duelpadarcade/Duelpad-Zen/source/configs/ergoSHIFTRev2/assets/ergoSHIFT-rev2-bare1.jpg

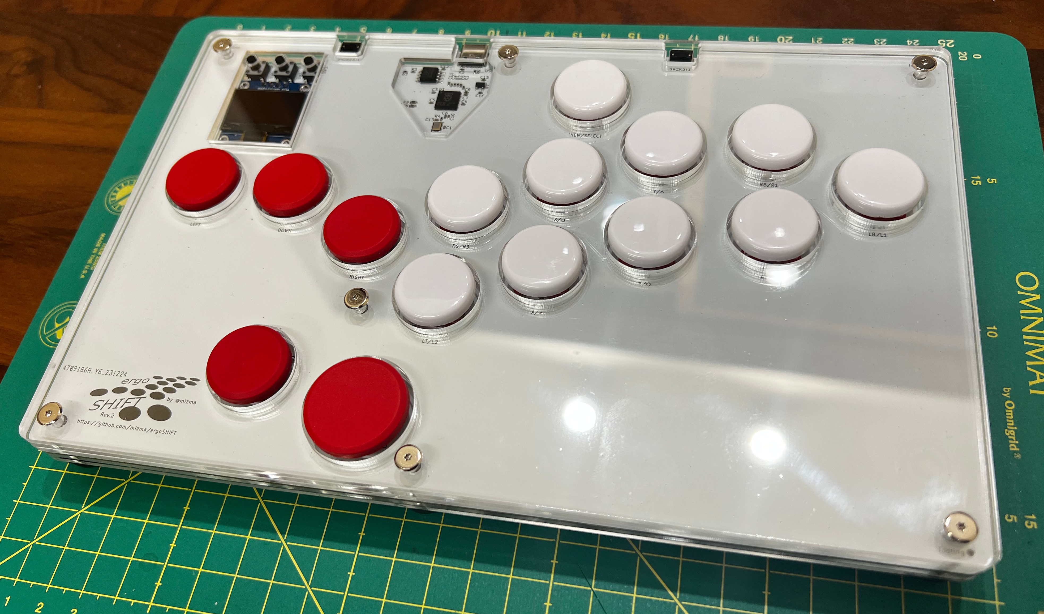
source/configs/ergoSHIFTRev2/assets/ergoSHIFT-rev2-bare1.jpg
