duelpadarcade/Duelpad-Zen/source/configs/Granola/assets/granola-trailmix.png

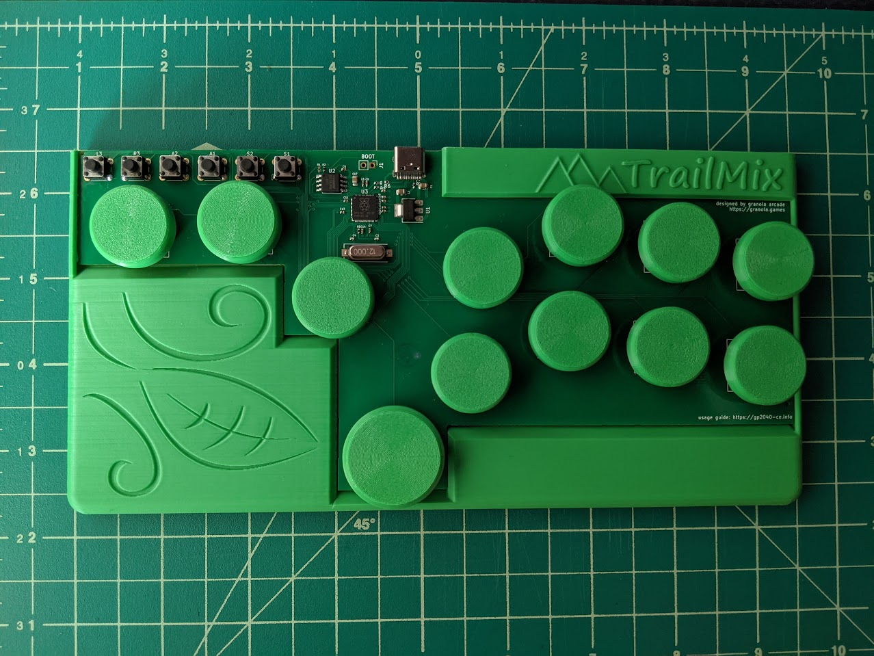
source/configs/Granola/assets/granola-trailmix.png
