duelpadarcade/Duelpad-Zen/source/configs/ARCController/assets/ARC Accessibility Controller 1.JPG

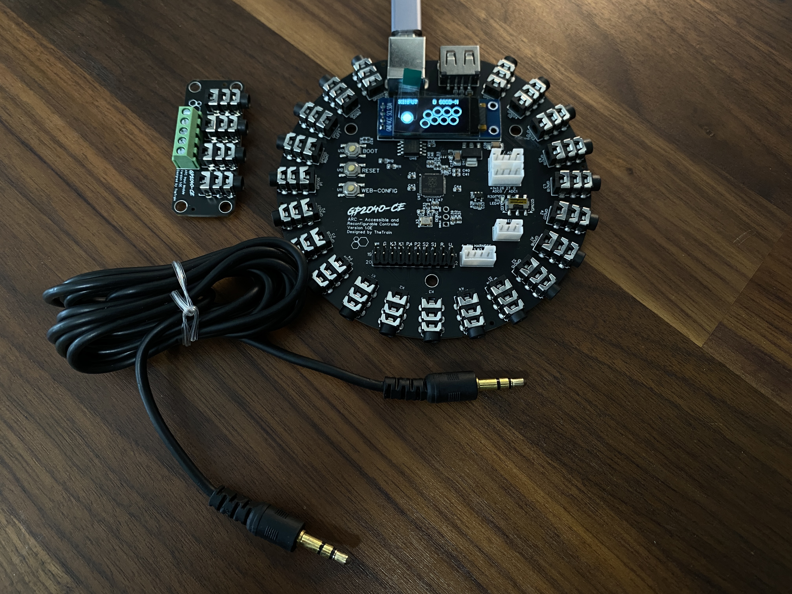
source/configs/ARCController/assets/ARC Accessibility Controller 1.JPG
