duelpadarcade/Duelpad-Zen/source/configs/ARCController/assets/ARC Accessibility Controller 2.JPG

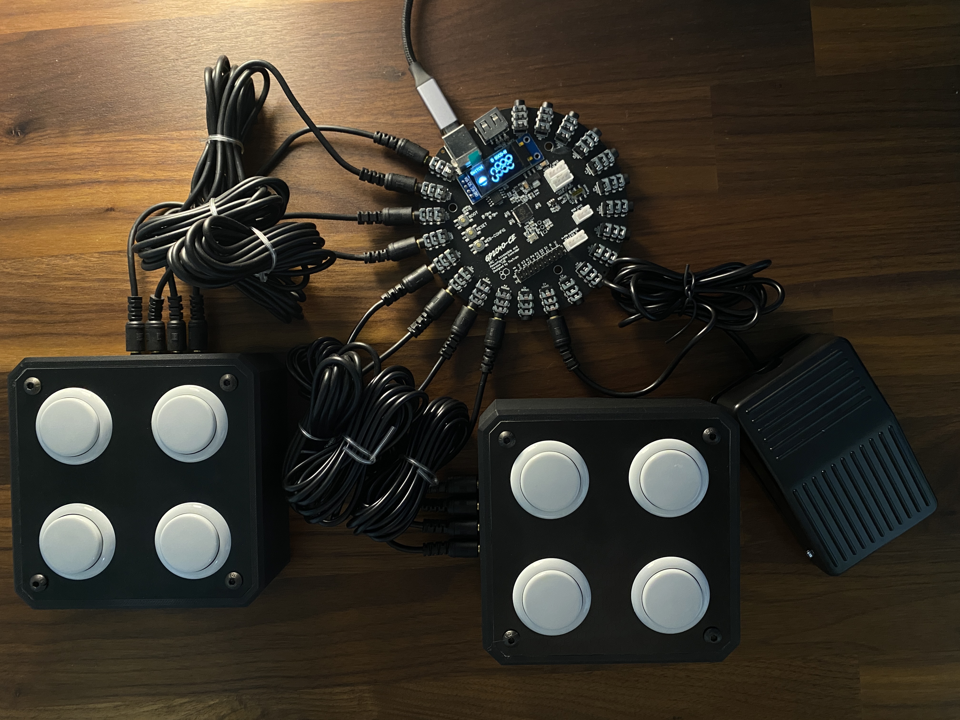
source/configs/ARCController/assets/ARC Accessibility Controller 2.JPG
