duelpadarcade/Duelpad-Zen/source/configs/ARCController/assets/ARC Accessibility Controller 3.JPG

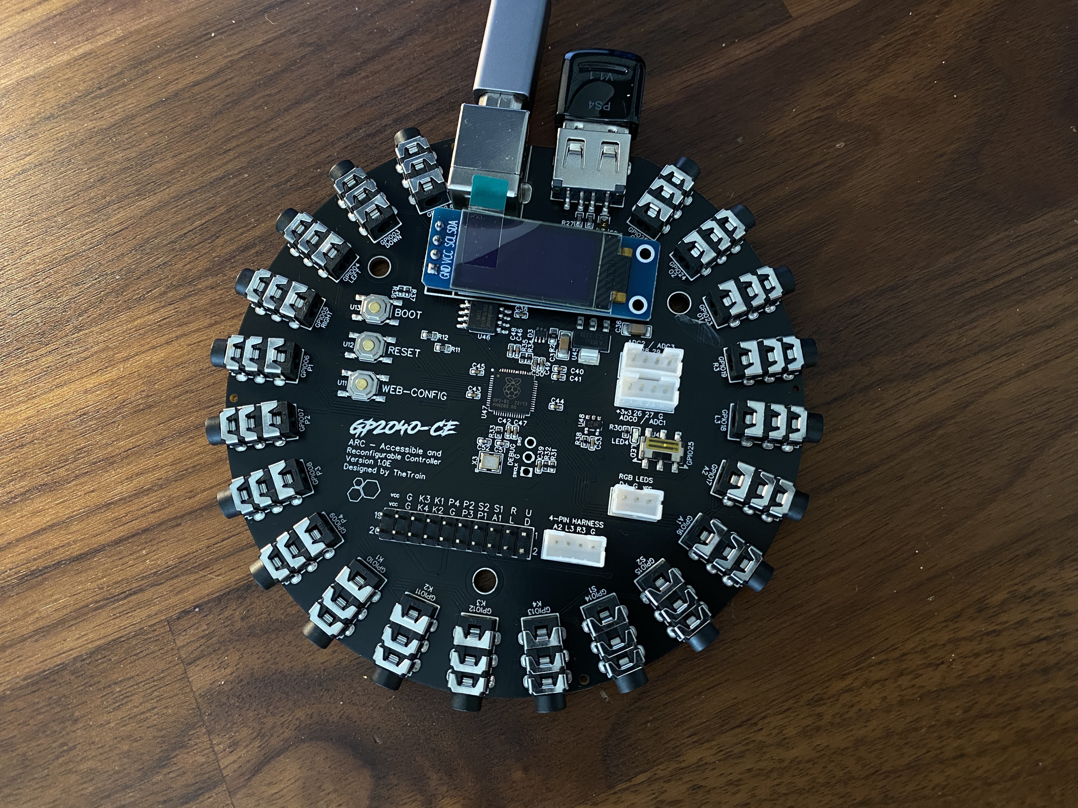
source/configs/ARCController/assets/ARC Accessibility Controller 3.JPG
