duelpadarcade/Duelpad-Zen/source/configs/BentoBox/assets/ScrubTier_Large.png

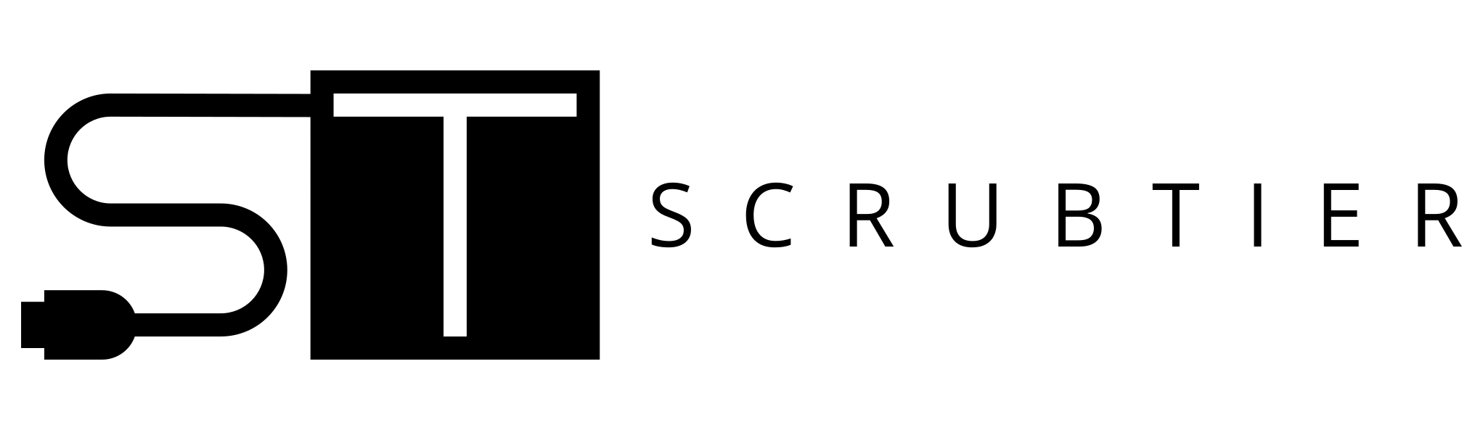
source/configs/BentoBox/assets/ScrubTier_Large.png
