duelpadarcade/Duelpad-Zen/source/configs/BentoBox/assets/ST_BentoBoxV1.png

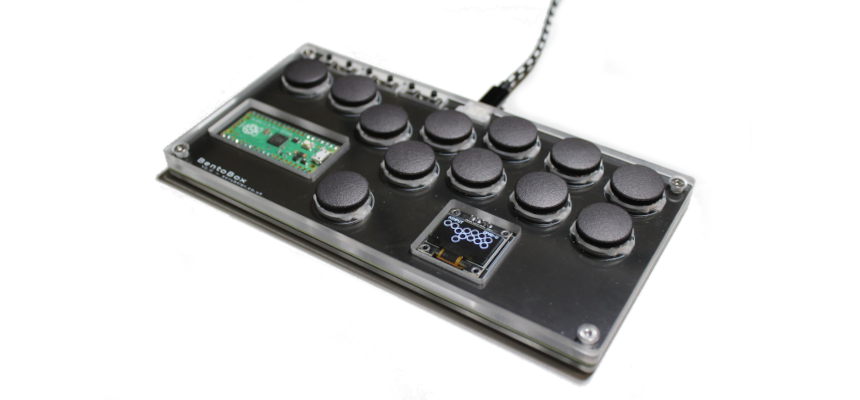
source/configs/BentoBox/assets/ST_BentoBoxV1.png
