duelpadarcade/Duelpad-Zen/source/configs/BentoBox/assets/ST_BentoBoxV2.png

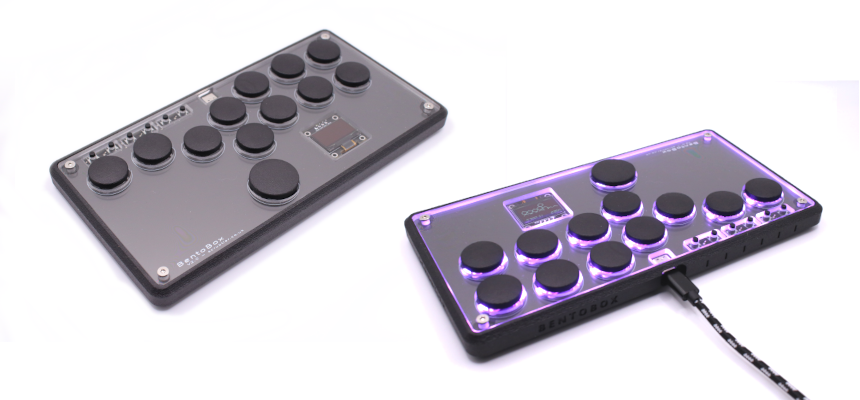
source/configs/BentoBox/assets/ST_BentoBoxV2.png
