duelpadarcade/Duelpad-Zen/source/configs/BentoBox/assets/ST_GGEZStick.png

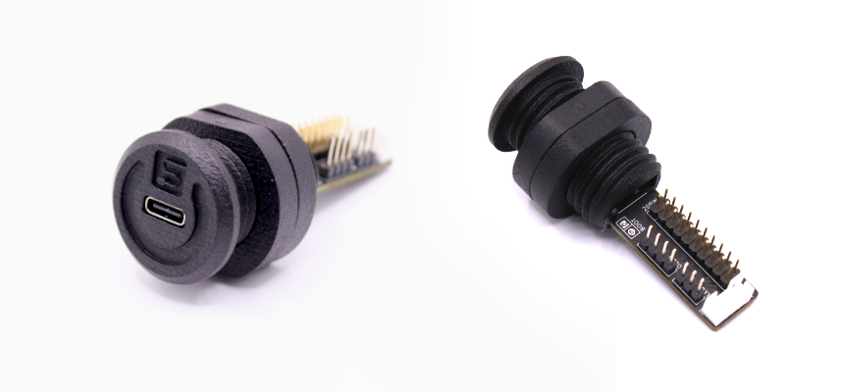
source/configs/BentoBox/assets/ST_GGEZStick.png
