duelpadarcade/Duelpad-Zen/source/configs/ergoSHIFTRev2/assets/ergoSHIFT-rev2-button-mapping.jpg

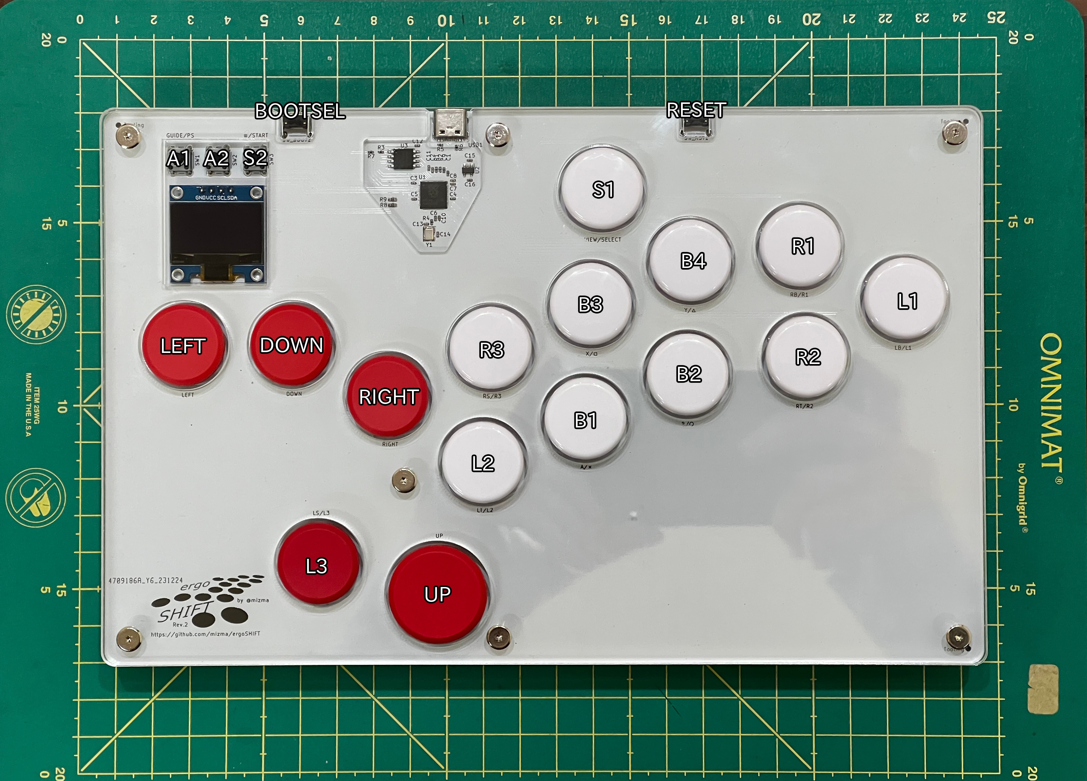
source/configs/ergoSHIFTRev2/assets/ergoSHIFT-rev2-button-mapping.jpg
