duelpadarcade/Duelpad-Zen/source/configs/FightboardV3/assets/FightboardV3.jpg

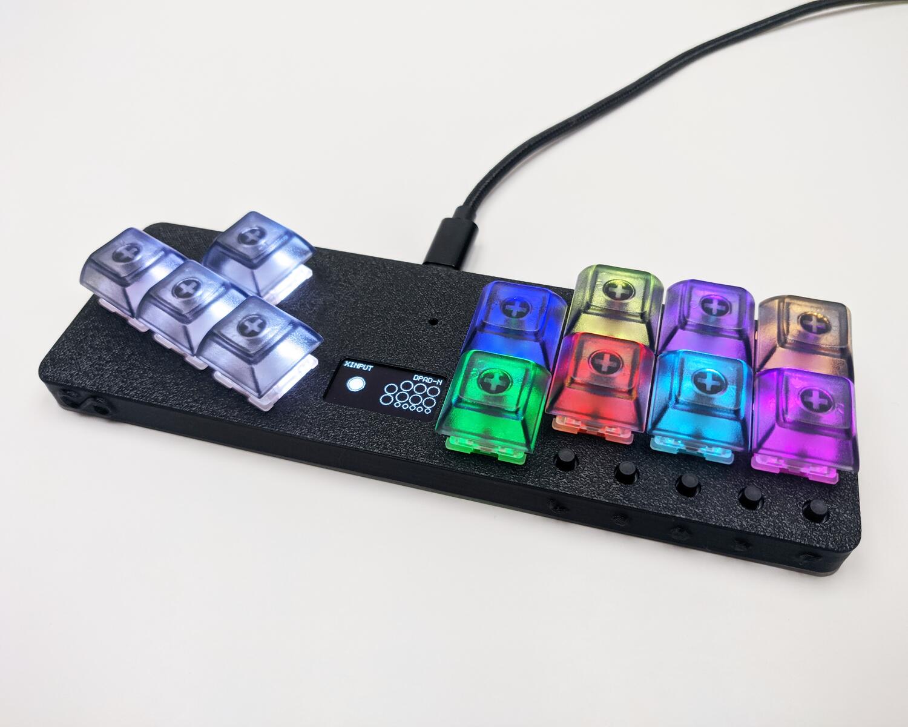
source/configs/FightboardV3/assets/FightboardV3.jpg
