duelpadarcade/Duelpad-Zen/source/configs/FightboardV3Mirrored/assets/FightboardV3Mirrored.jpg

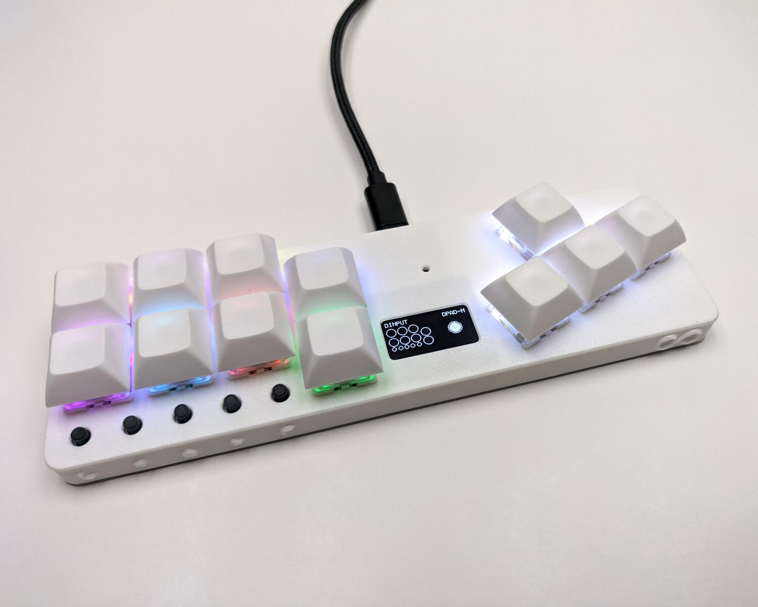
source/configs/FightboardV3Mirrored/assets/FightboardV3Mirrored.jpg
