duelpadarcade/Duelpad-Zen/source/configs/FlatboxRev5/assets/Flatbox-rev5.jpg

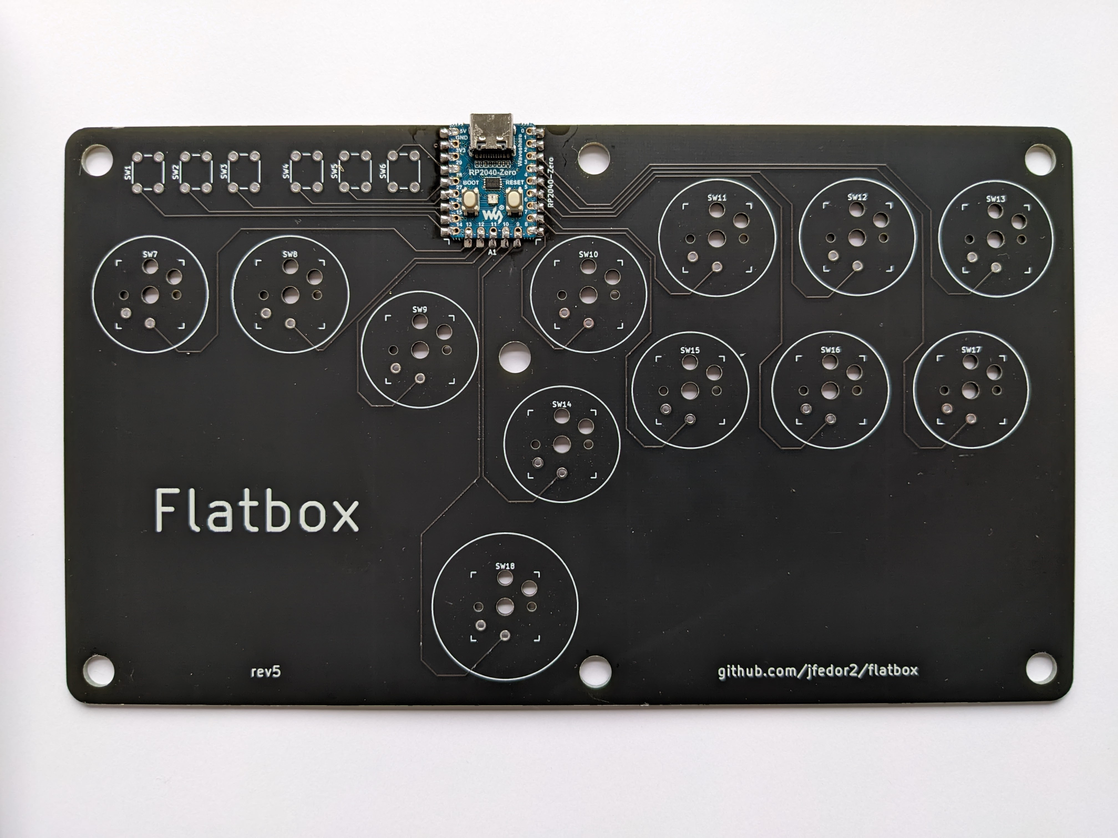
source/configs/FlatboxRev5/assets/Flatbox-rev5.jpg
