duelpadarcade/Duelpad-Zen/source/configs/FlatboxRev5RGB/assets/Flatbox-rev5-rgb.jpg

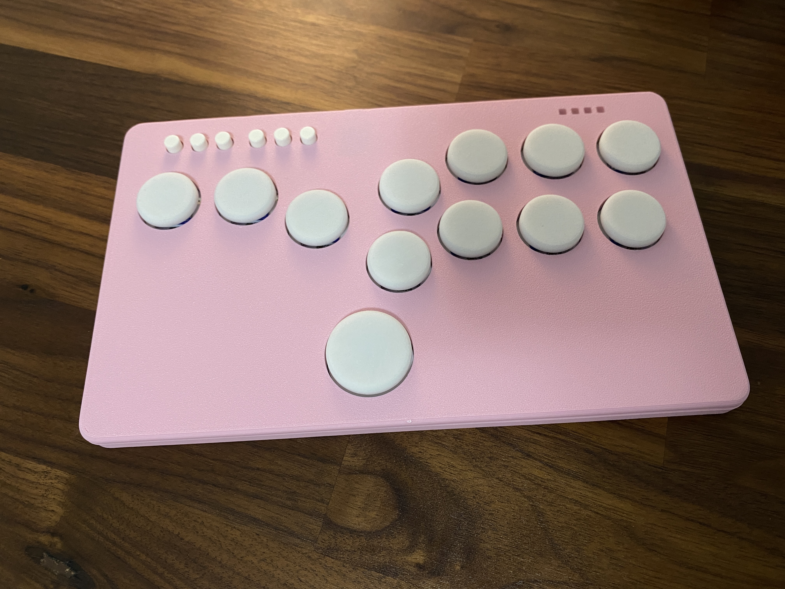
source/configs/FlatboxRev5RGB/assets/Flatbox-rev5-rgb.jpg
