duelpadarcade/Duelpad-Zen/source/configs/FlatboxRev5Southpaw/assets/Flatbox-rev5.jpg

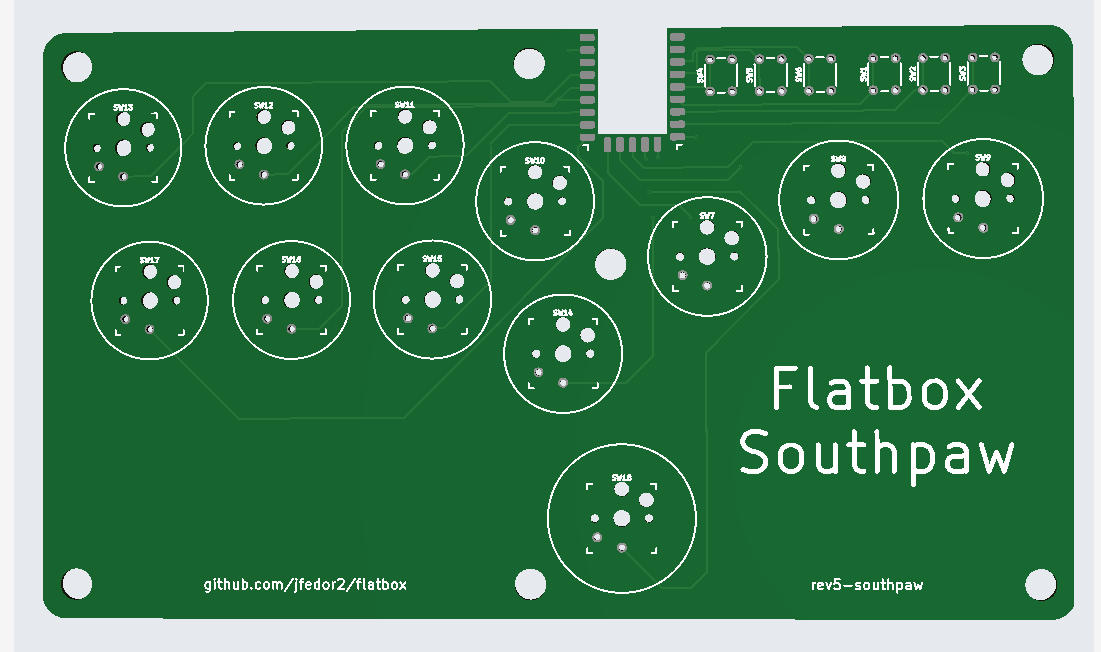
source/configs/FlatboxRev5Southpaw/assets/Flatbox-rev5.jpg
