duelpadarcade/Duelpad-Zen/source/configs/FlatboxRev5USBPassthrough/assets/Flatbox-rev5-USB-Passthrough.jpg

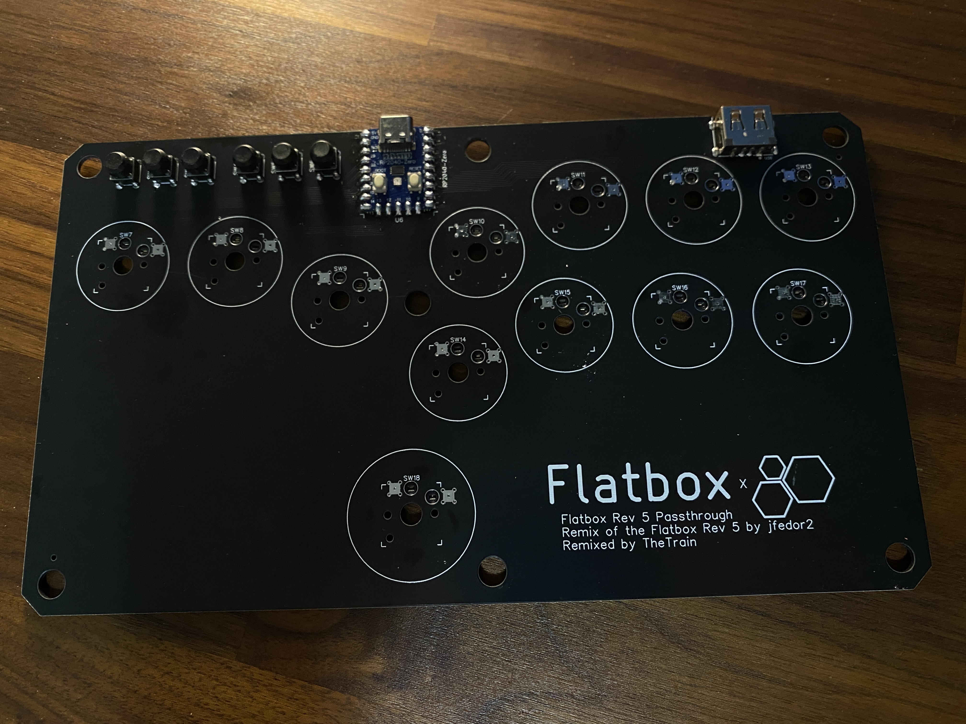
source/configs/FlatboxRev5USBPassthrough/assets/Flatbox-rev5-USB-Passthrough.jpg
