duelpadarcade/Duelpad-Zen/source/configs/Granola/assets/granola-summit.png

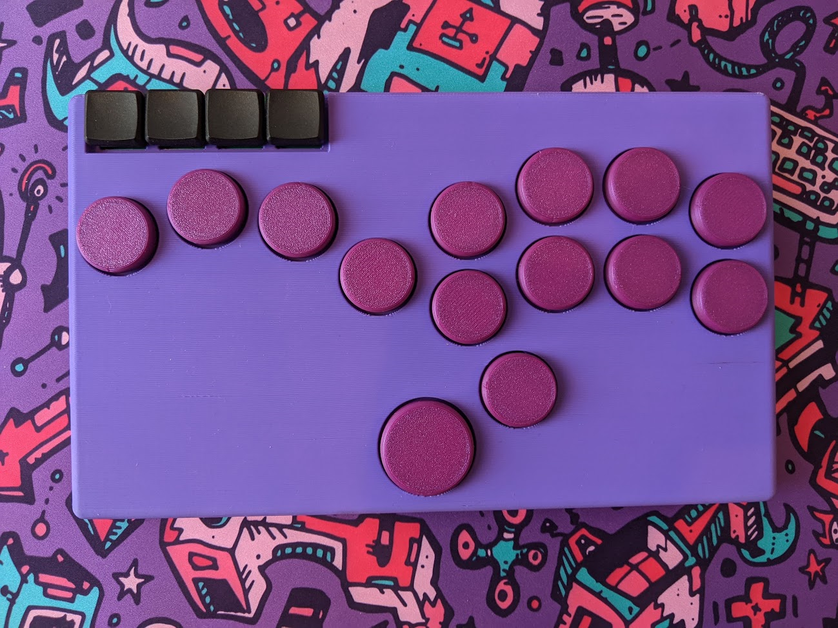
source/configs/Granola/assets/granola-summit.png
