duelpadarcade/Duelpad-Zen/source/configs/Haute42COSMOX/assets/Haute42_G12.png

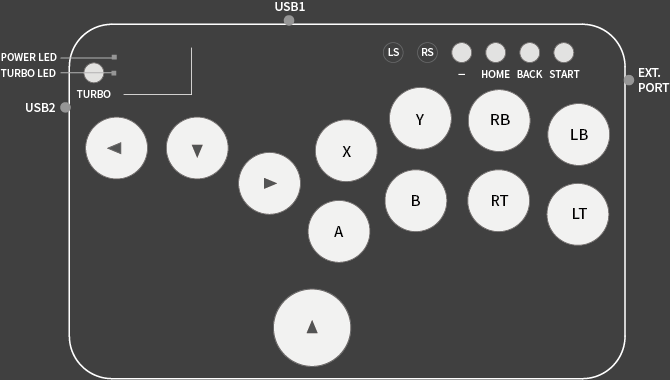
source/configs/Haute42COSMOX/assets/Haute42_G12.png
