duelpadarcade/Duelpad-Zen/source/configs/Haute42COSMOX/assets/Haute42_G13.png

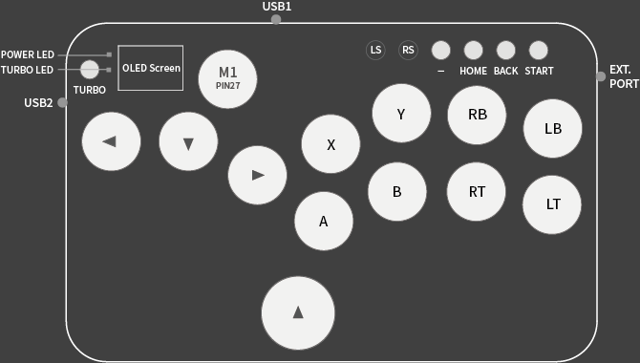
source/configs/Haute42COSMOX/assets/Haute42_G13.png
