duelpadarcade/Duelpad-Zen/source/configs/Haute42COSMOX/assets/Haute42_G16.png

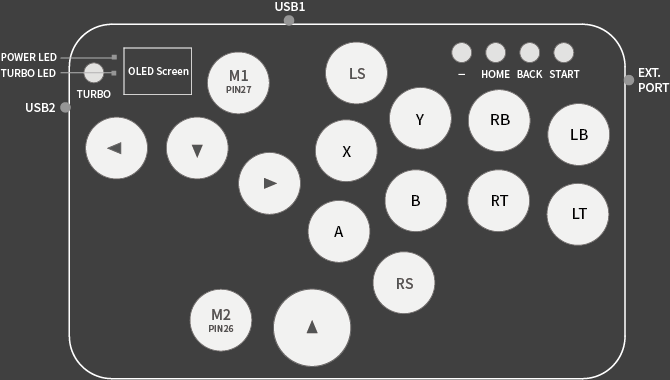
source/configs/Haute42COSMOX/assets/Haute42_G16.png
