duelpadarcade/Duelpad-Zen/source/configs/Haute42COSMOX/assets/Haute42_G_series.png

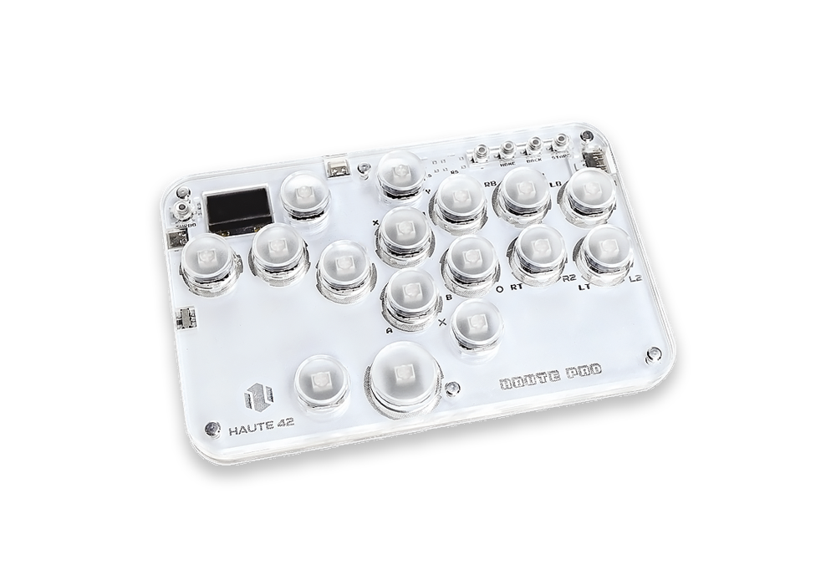
source/configs/Haute42COSMOX/assets/Haute42_G_series.png
