duelpadarcade/Duelpad-Zen/source/configs/Haute42COSMOX/assets/Haute42_Mini.png

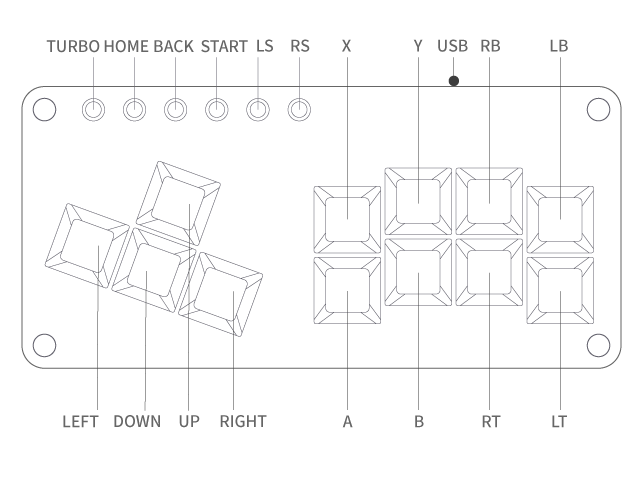
source/configs/Haute42COSMOX/assets/Haute42_Mini.png
