duelpadarcade/Duelpad-Zen/source/configs/Haute42COSMOX/assets/Haute42_Mini_series.png

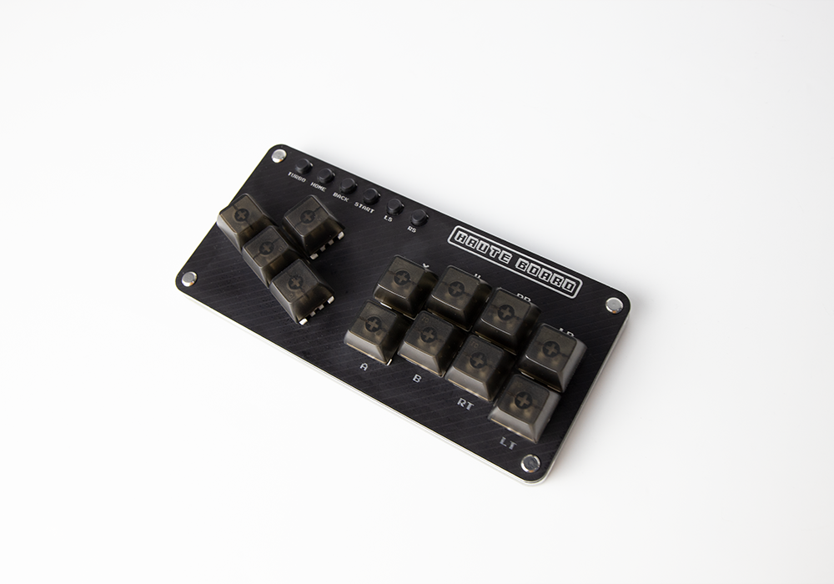
source/configs/Haute42COSMOX/assets/Haute42_Mini_series.png
