duelpadarcade/Duelpad-Zen/source/configs/Haute42COSMOX/assets/Haute42_T13.png

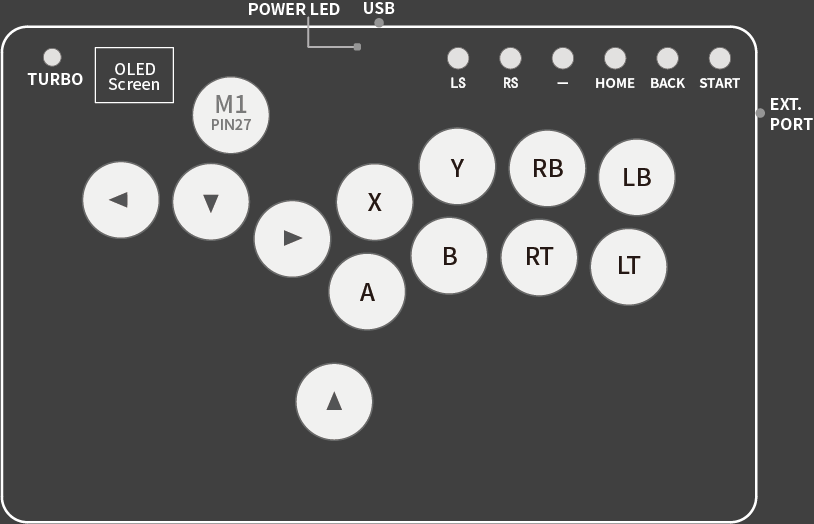
source/configs/Haute42COSMOX/assets/Haute42_T13.png
