duelpadarcade/Duelpad-Zen/source/configs/Haute42COSMOX/assets/Haute42_T16.png

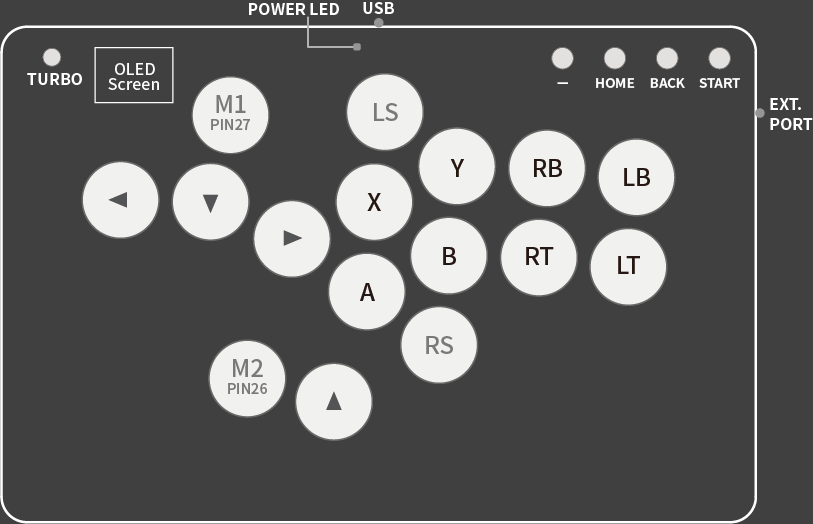
source/configs/Haute42COSMOX/assets/Haute42_T16.png
