duelpadarcade/Duelpad-Zen/source/configs/KB2040/assets/PinMapping.png

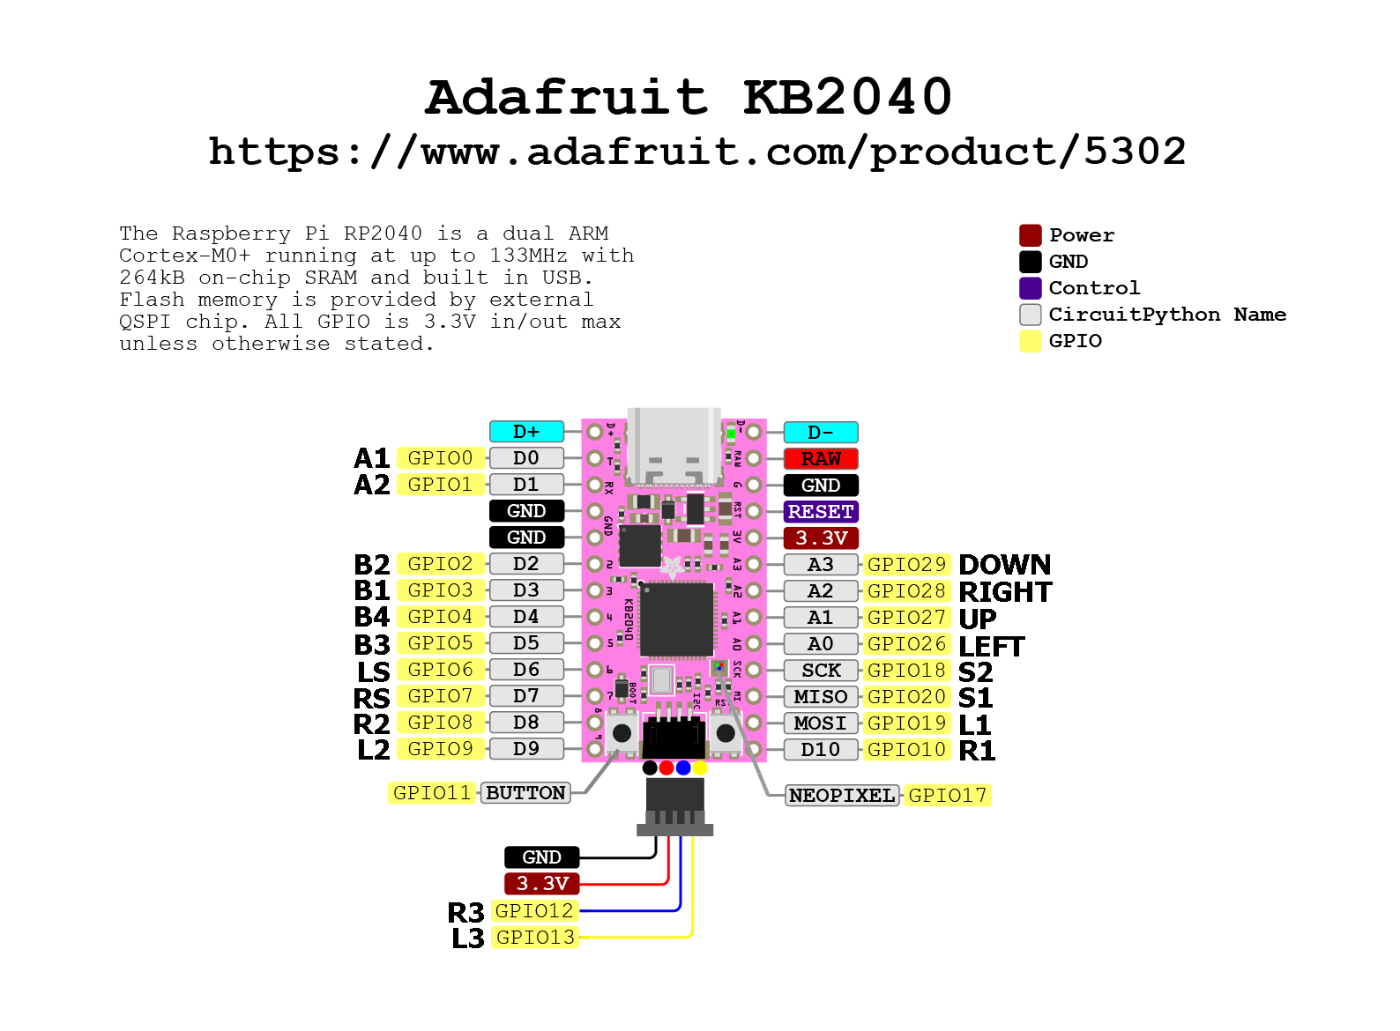
source/configs/KB2040/assets/PinMapping.png
