duelpadarcade/Duelpad-Zen/source/configs/KeyboardConverter/assets/WaveshareRP2040Zero.png

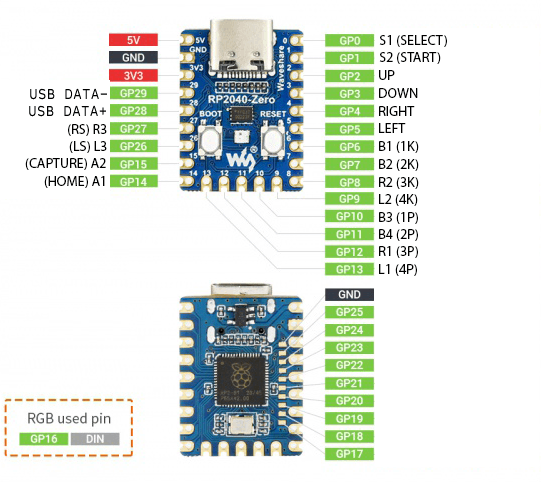
source/configs/KeyboardConverter/assets/WaveshareRP2040Zero.png
