duelpadarcade/Duelpad-Zen/source/configs/Liatris/assets/Liatris.png

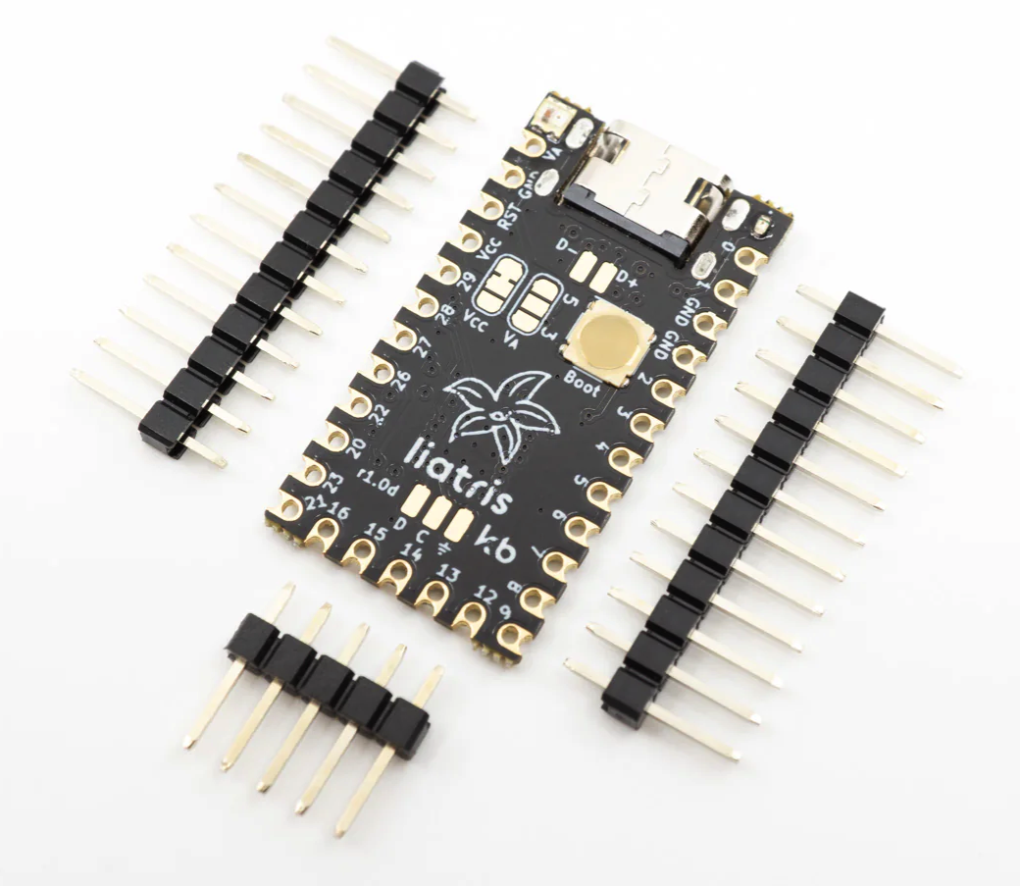
source/configs/Liatris/assets/Liatris.png
