duelpadarcade/Duelpad-Zen/source/configs/MavercadeRev2/assets/Rev2_config_pic.jpg

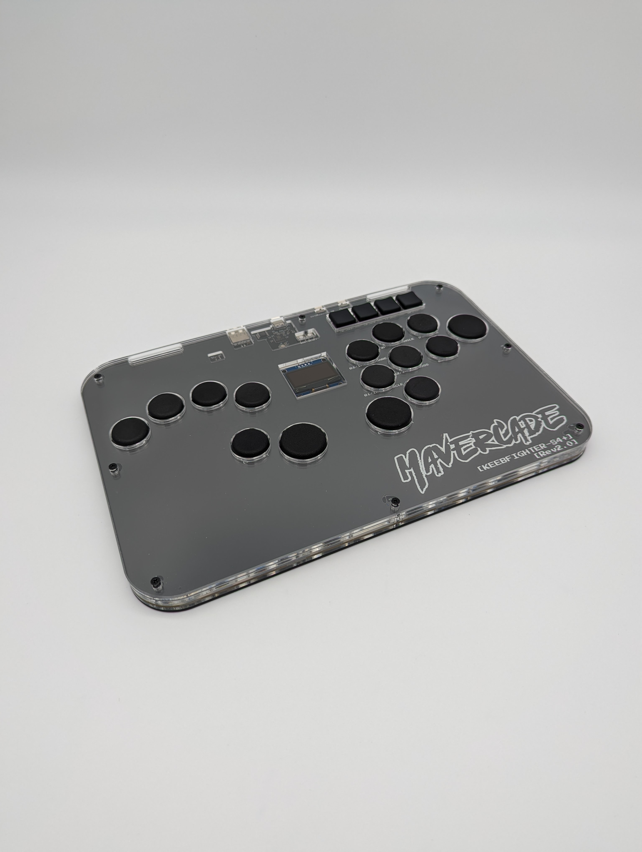
source/configs/MavercadeRev2/assets/Rev2_config_pic.jpg
