duelpadarcade/Duelpad-Zen/source/configs/MiSTercadeV2/assets/MistercadeV2.jpg

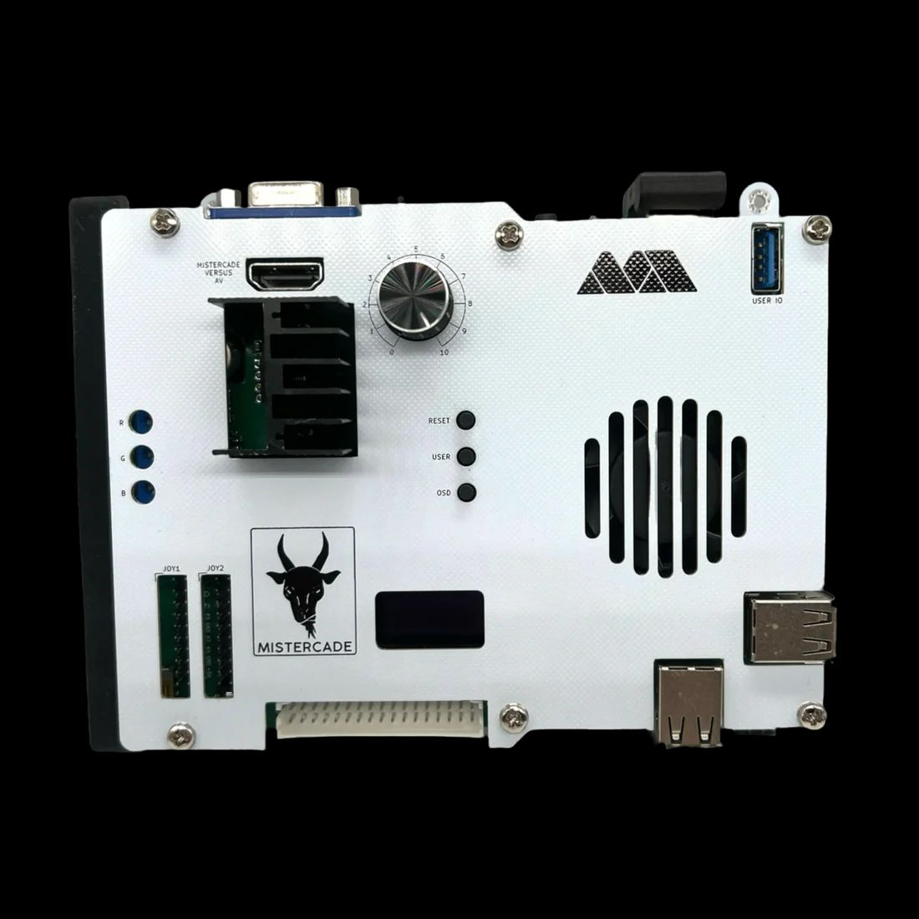
source/configs/MiSTercadeV2/assets/MistercadeV2.jpg
