duelpadarcade/Duelpad-Zen/source/configs/OpenCore0/assets/Open_Core0.jpg

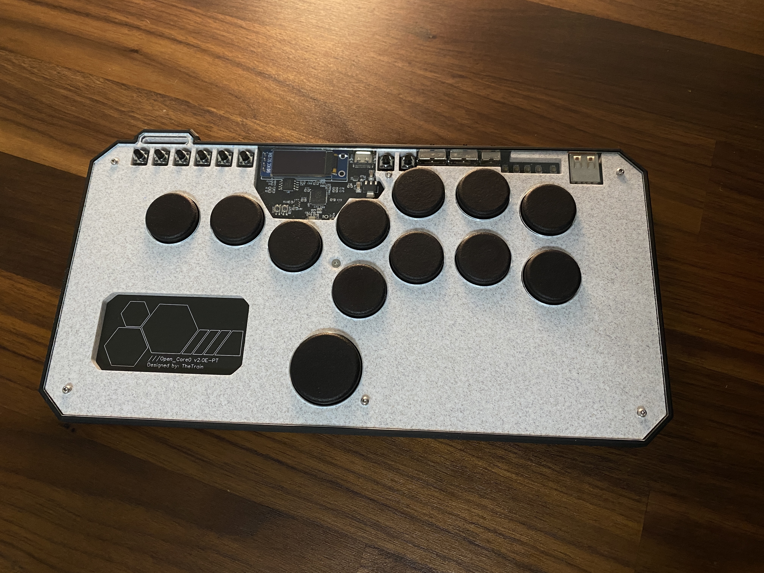
source/configs/OpenCore0/assets/Open_Core0.jpg
