duelpadarcade/Duelpad-Zen/source/configs/OpenCore0/assets/Open_Core0_2.jpg

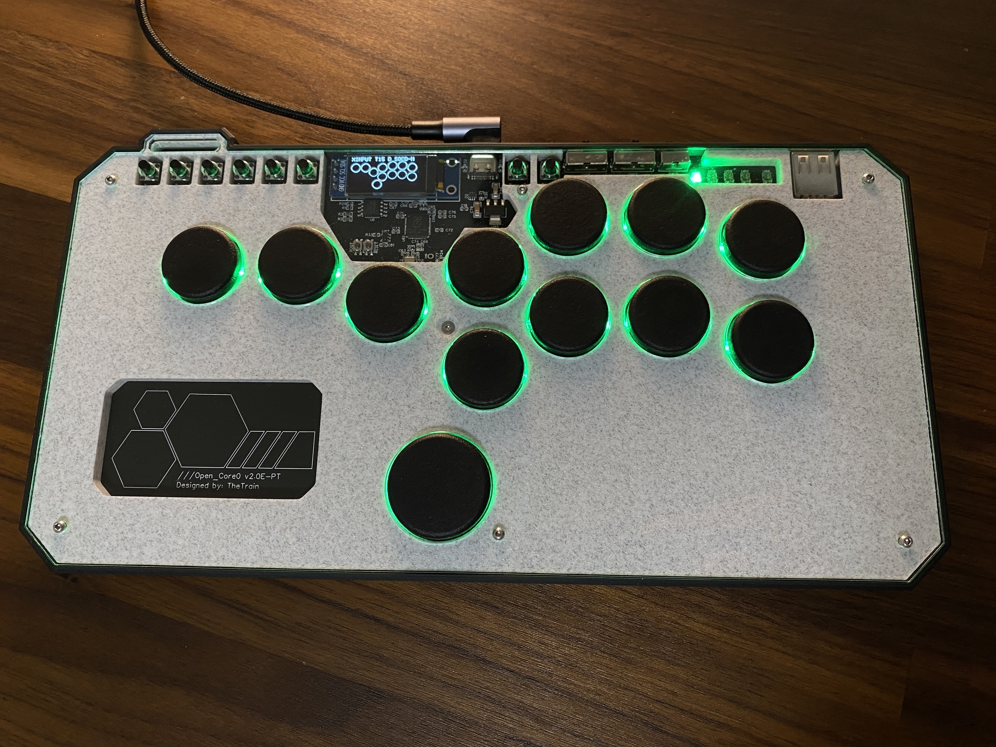
source/configs/OpenCore0/assets/Open_Core0_2.jpg
