duelpadarcade/Duelpad-Zen/source/configs/OpenCore0/assets/Open_Core0_layout.png

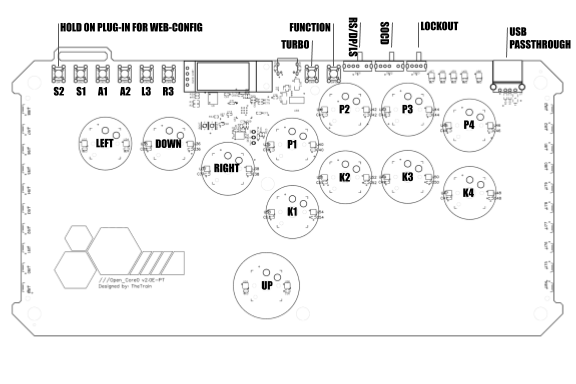
source/configs/OpenCore0/assets/Open_Core0_layout.png
