duelpadarcade/Duelpad-Zen/source/configs/OpenCore0/assets/Open_Core0_pin_mapping.png

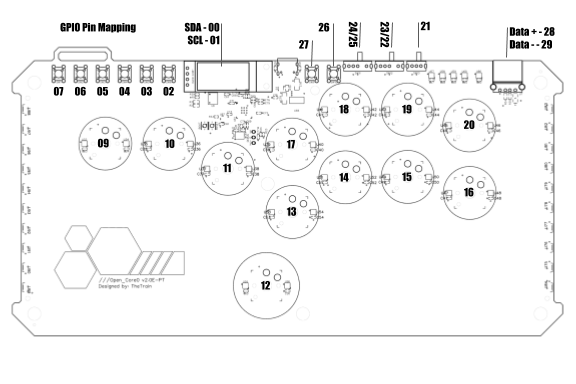
source/configs/OpenCore0/assets/Open_Core0_pin_mapping.png
