duelpadarcade/Duelpad-Zen/source/configs/OpenCore0WASD/assets/Open_Core0_WASD.jpg

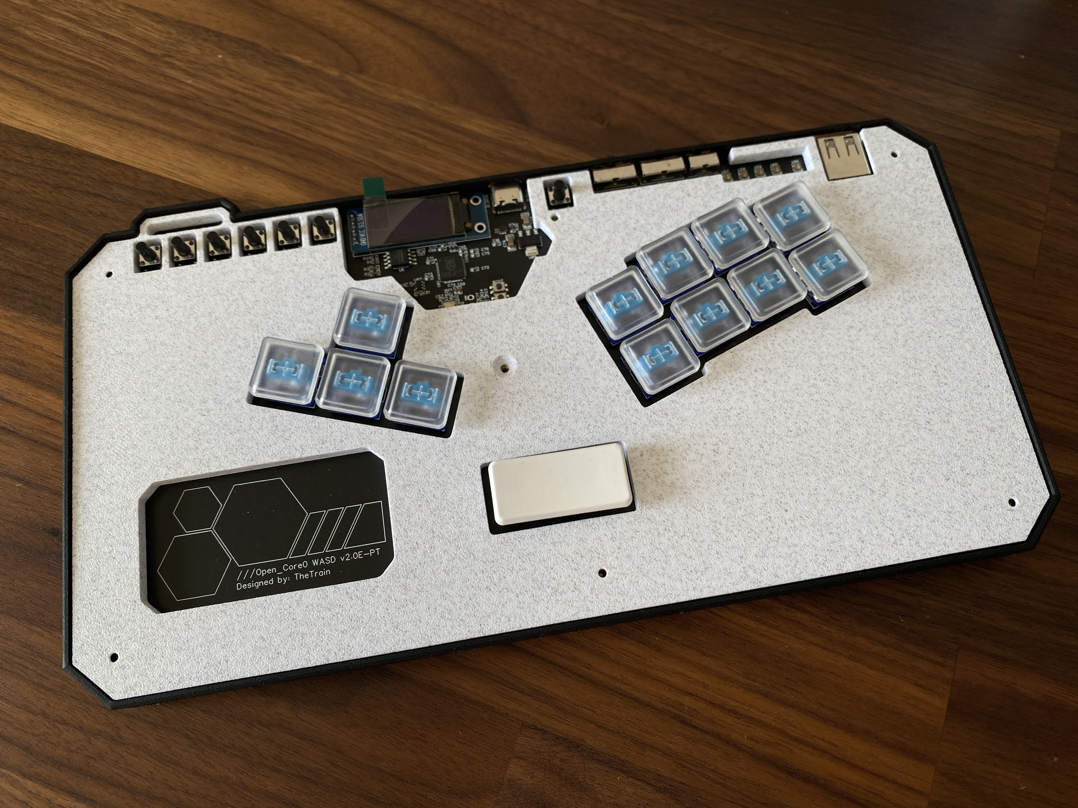
source/configs/OpenCore0WASD/assets/Open_Core0_WASD.jpg
