duelpadarcade/Duelpad-Zen/source/configs/OpenCore0WASD/assets/Open_Core0_WASD_pinout.png

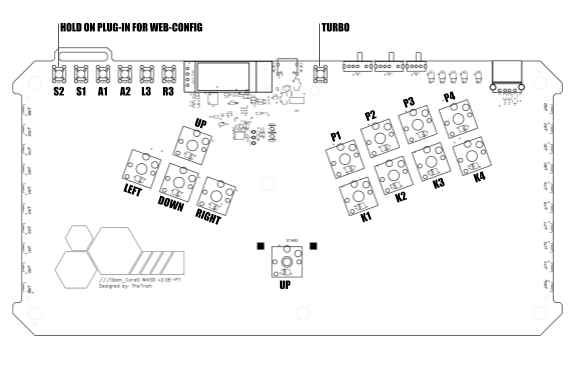
source/configs/OpenCore0WASD/assets/Open_Core0_WASD_pinout.png
