duelpadarcade/Duelpad-Zen/source/configs/OSUMGP-RP2040/osumgp-rp2040_0.4b-real.jpg

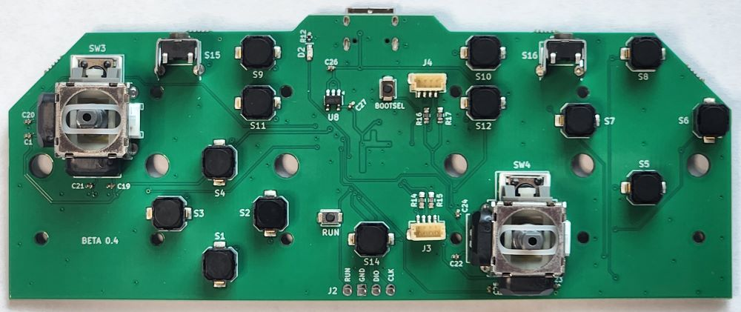
source/configs/OSUMGP-RP2040/osumgp-rp2040_0.4b-real.jpg
