duelpadarcade/Duelpad-Zen/source/configs/Pico/assets/PinMapping.png

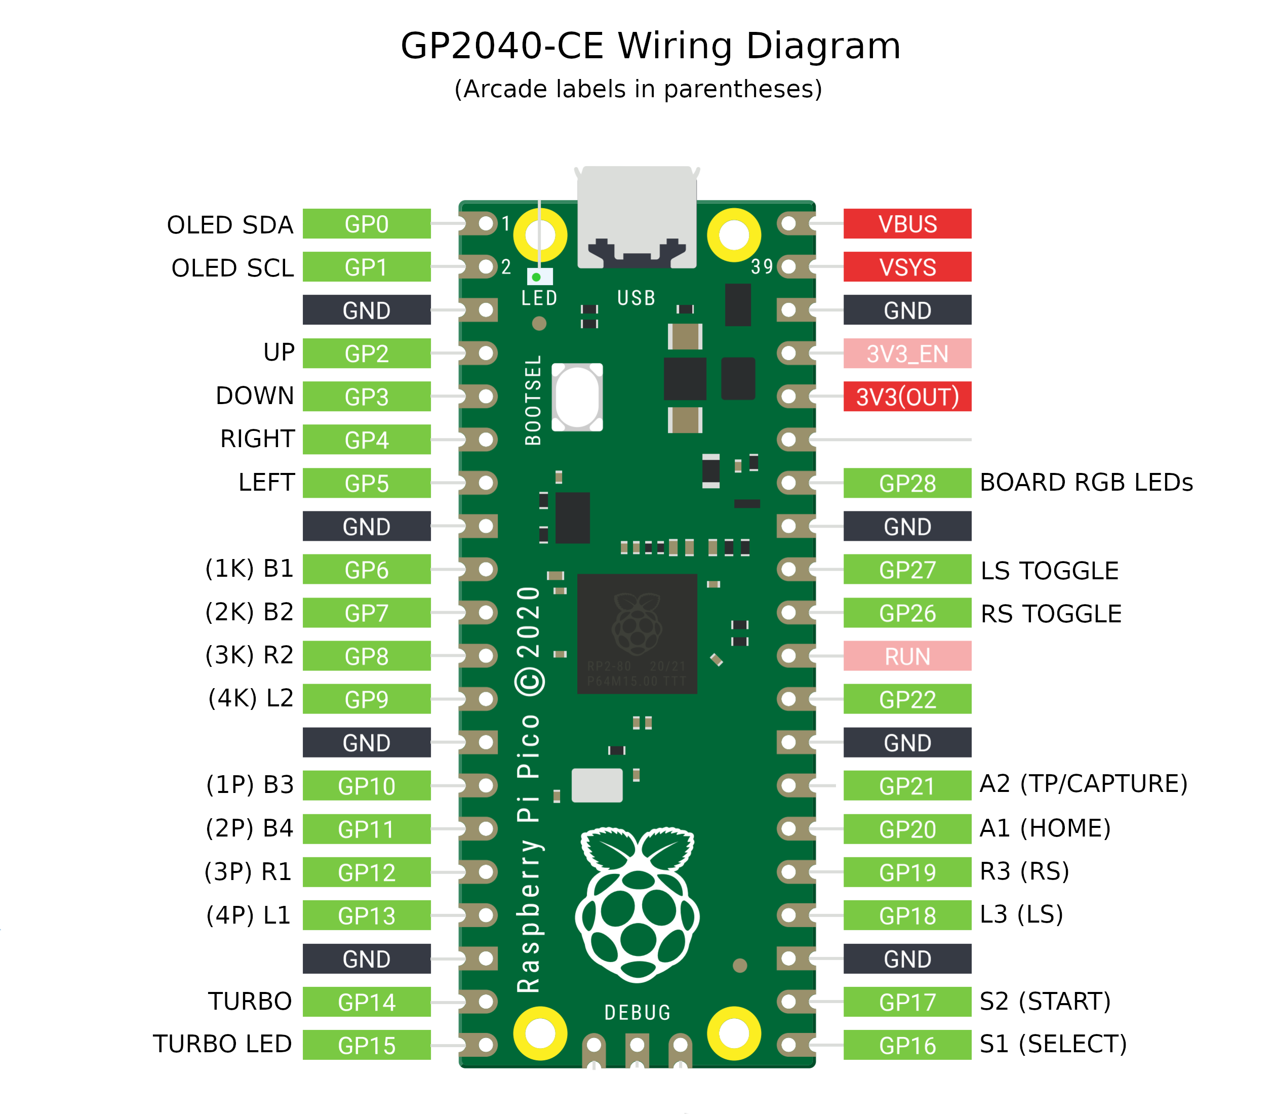
source/configs/Pico/assets/PinMapping.png
