duelpadarcade/Duelpad-Zen/source/configs/PicoFightingBoard/assets/PicoFightingBoard_v1.1.jpg

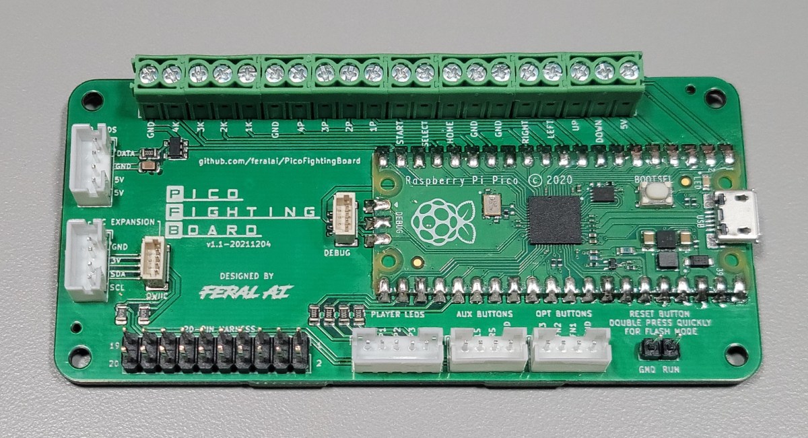
source/configs/PicoFightingBoard/assets/PicoFightingBoard_v1.1.jpg
