duelpadarcade/Duelpad-Zen/source/configs/RanaTadpole/assets/RanaTadpole1.jpg

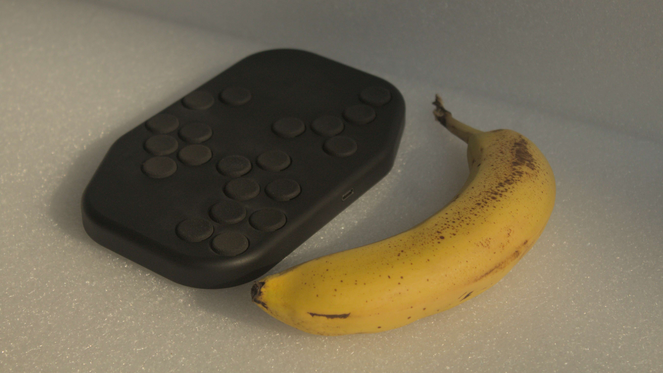
source/configs/RanaTadpole/assets/RanaTadpole1.jpg
