duelpadarcade/Duelpad-Zen/source/configs/RanaTadpole/assets/RanaTadpole2.jpg

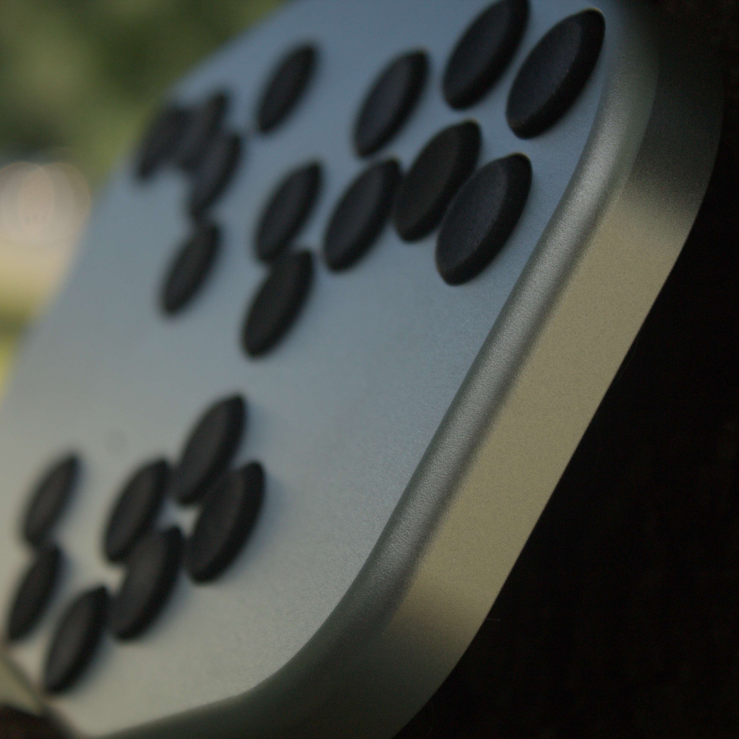
source/configs/RanaTadpole/assets/RanaTadpole2.jpg
