duelpadarcade/Duelpad-Zen/source/configs/RanaTadpole/assets/RanaTadpole_buttons.png

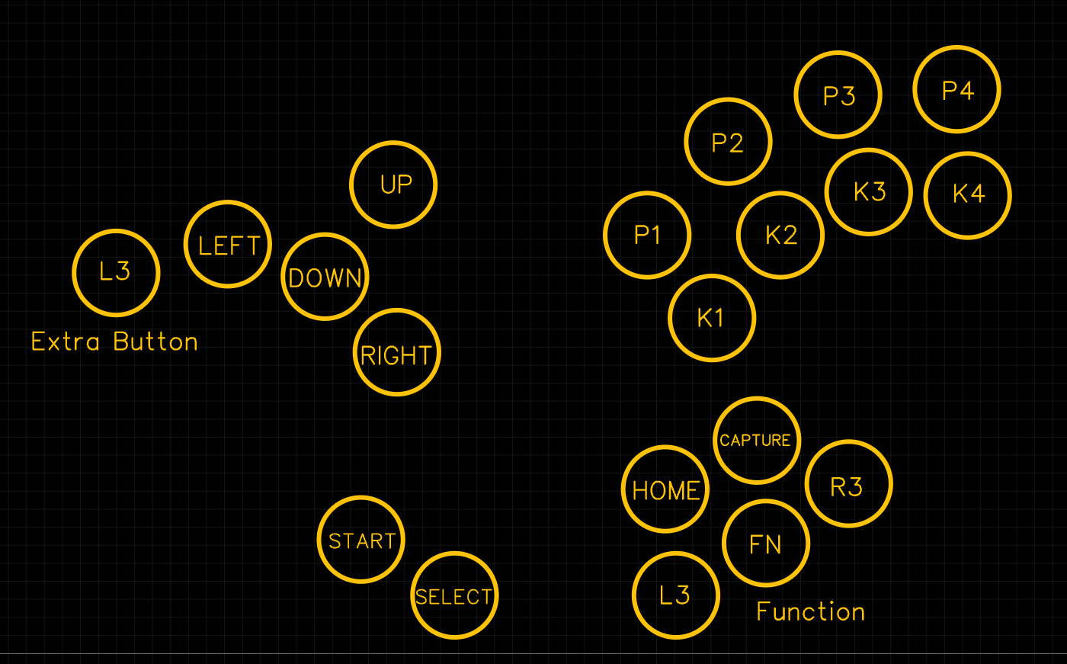
source/configs/RanaTadpole/assets/RanaTadpole_buttons.png
