duelpadarcade/Duelpad-Zen/source/configs/ReflexEncodeV2.0/assets/ReflexBoard_V2.png

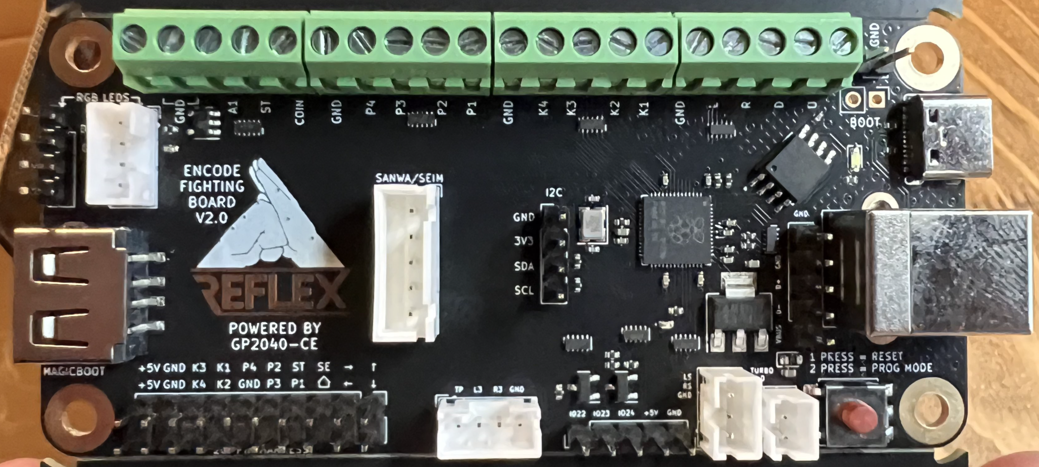
source/configs/ReflexEncodeV2.0/assets/ReflexBoard_V2.png
