duelpadarcade/Duelpad-Zen/source/configs/RP2040AdvancedBreakoutBoard/assets/RP2040AdvancedBreakoutBoard.jpg

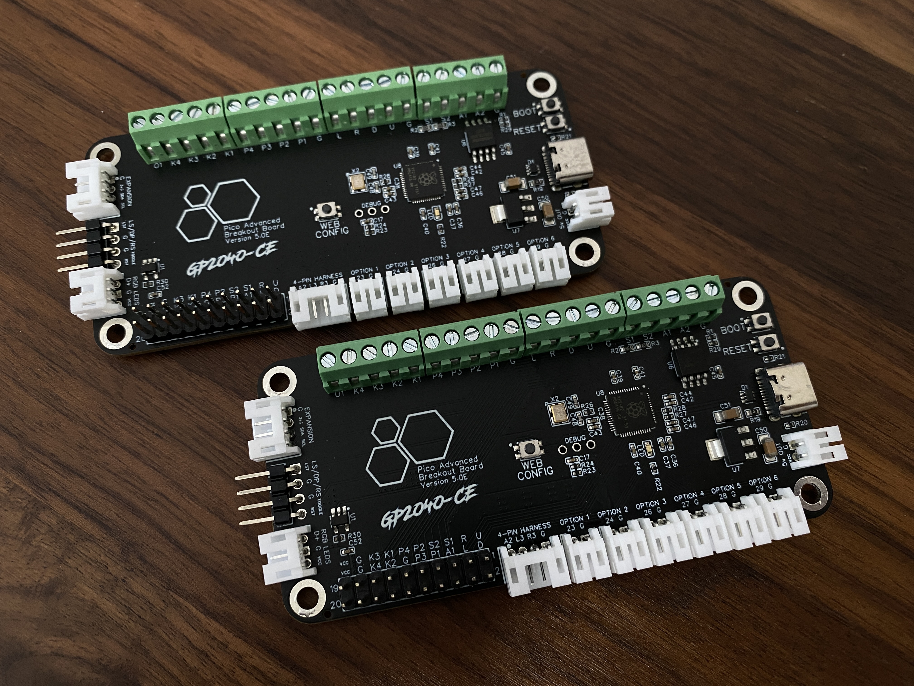
source/configs/RP2040AdvancedBreakoutBoard/assets/RP2040AdvancedBreakoutBoard.jpg
