duelpadarcade/Duelpad-Zen/source/configs/RP2040AdvancedBreakoutBoard/assets/RP2040AdvancedBreakoutBoard_pinout.png

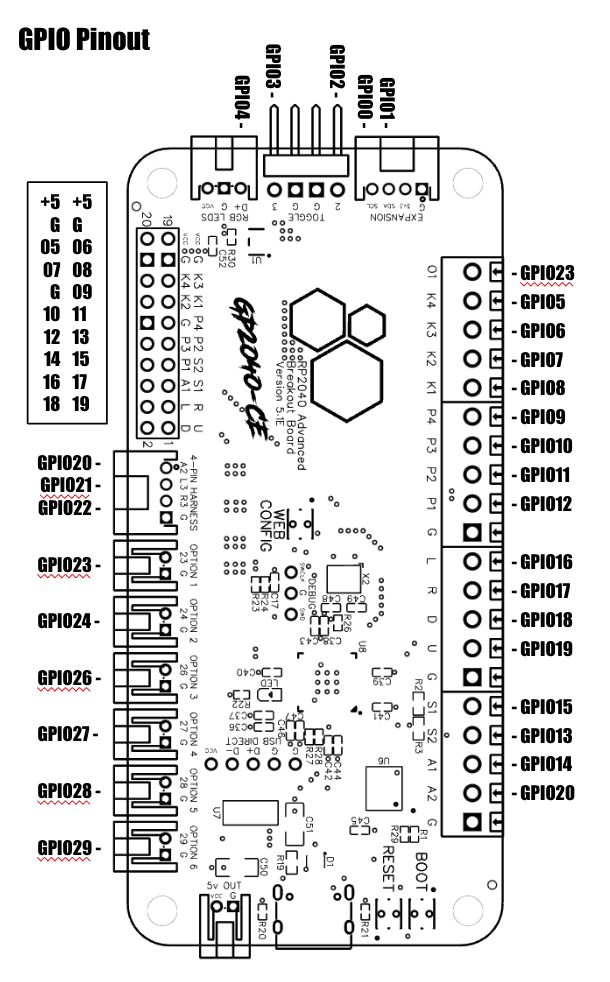
source/configs/RP2040AdvancedBreakoutBoard/assets/RP2040AdvancedBreakoutBoard_pinout.png
