duelpadarcade/Duelpad-Zen/source/configs/RP2040AdvancedBreakoutBoardUSBPassthrough/assets/RP2040 Advanced Breakout Board - Passthrough.jpg

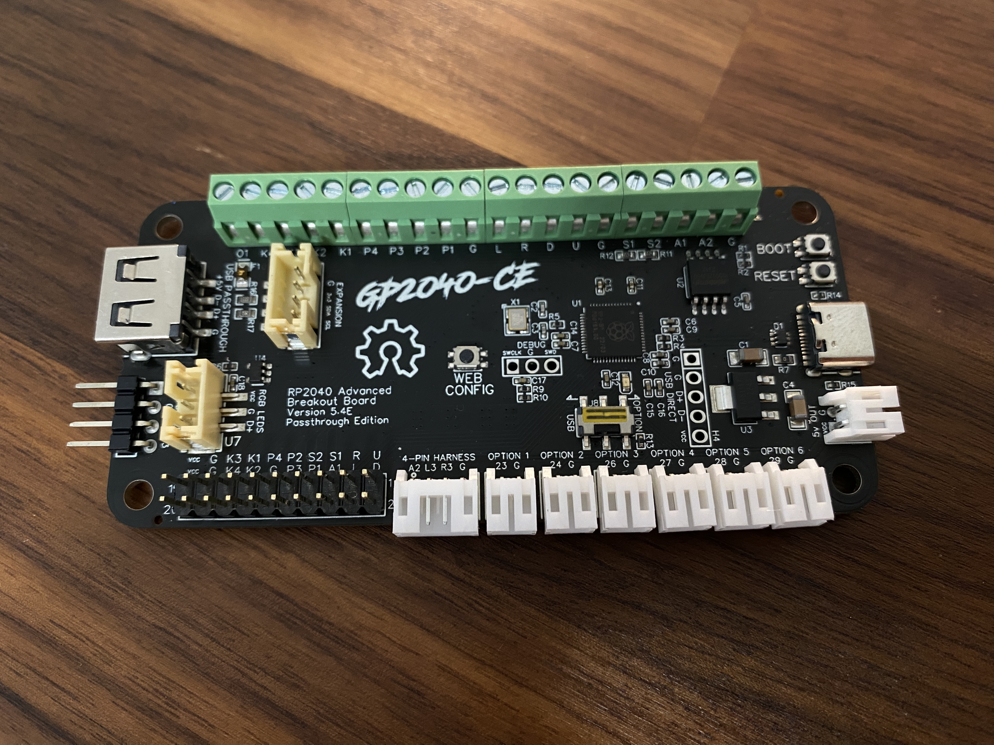
source/configs/RP2040AdvancedBreakoutBoardUSBPassthrough/assets/RP2040 Advanced Breakout Board - Passthrough.jpg
