duelpadarcade/Duelpad-Zen/source/configs/RP2040MiniBreakoutBoard/assets/RP2040MiniBreakoutBoard.jpg

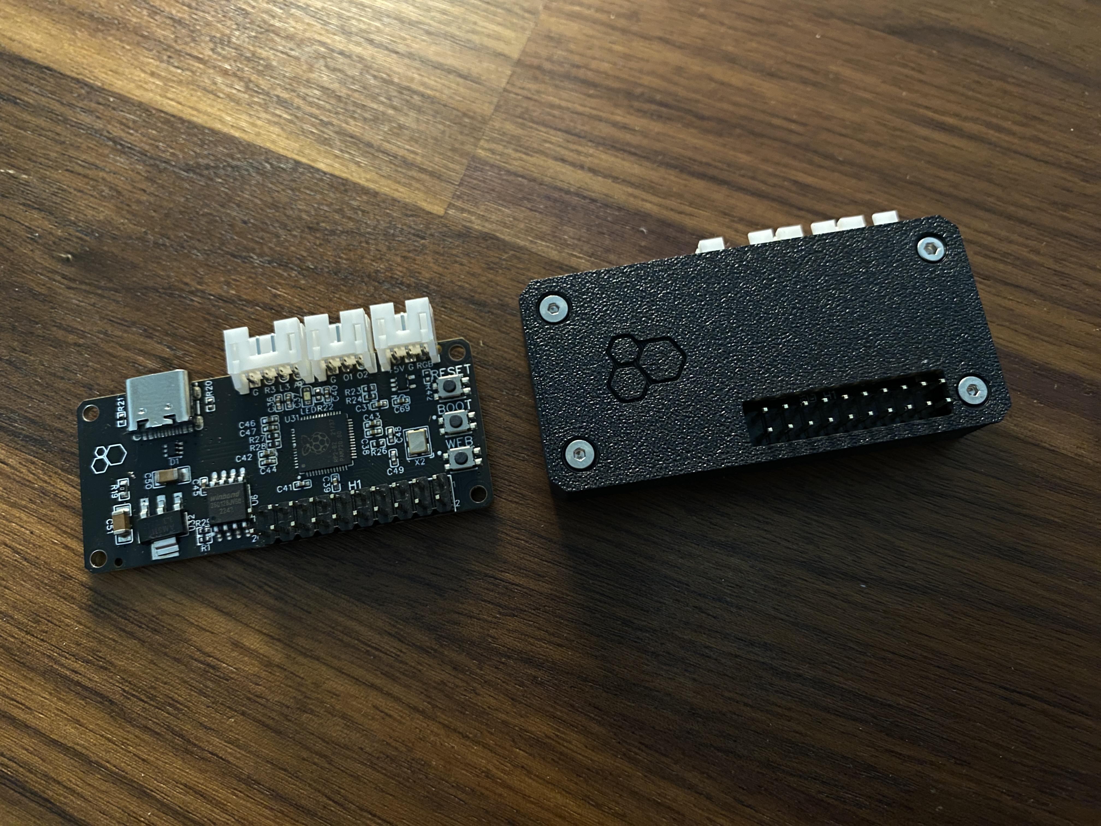
source/configs/RP2040MiniBreakoutBoard/assets/RP2040MiniBreakoutBoard.jpg
