duelpadarcade/Duelpad-Zen/source/configs/SGFDevices/assets/SGF_Controller.png

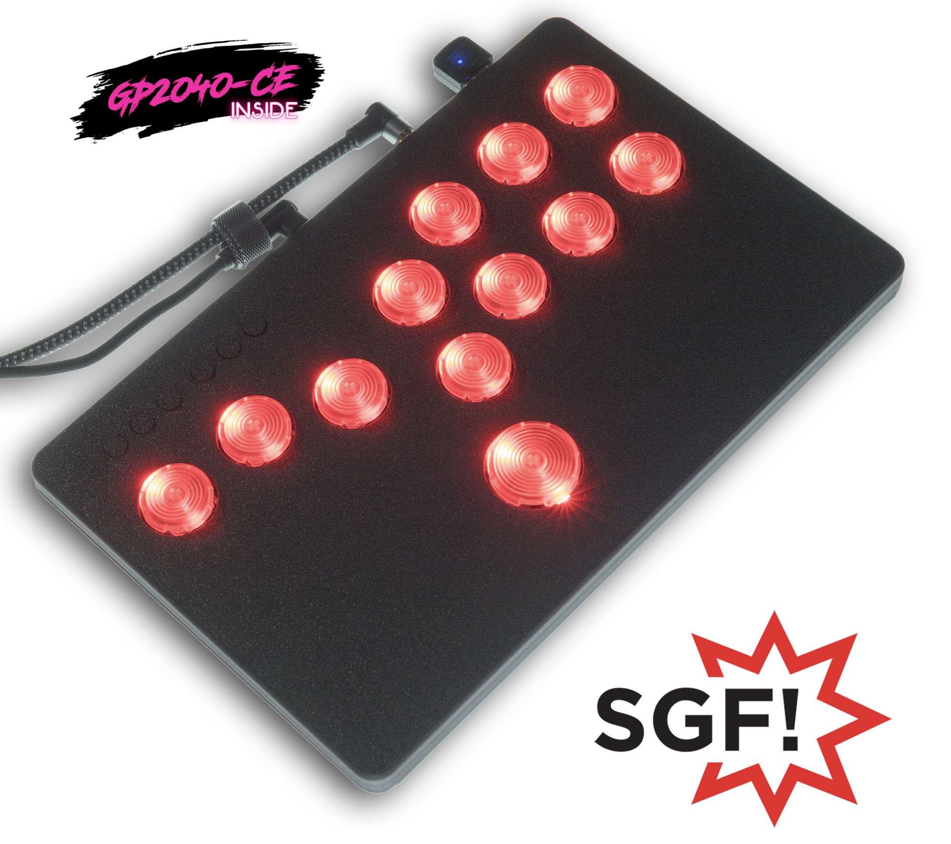
source/configs/SGFDevices/assets/SGF_Controller.png
