duelpadarcade/Duelpad-Zen/source/configs/SGFDevices/assets/SGF_Layout.png

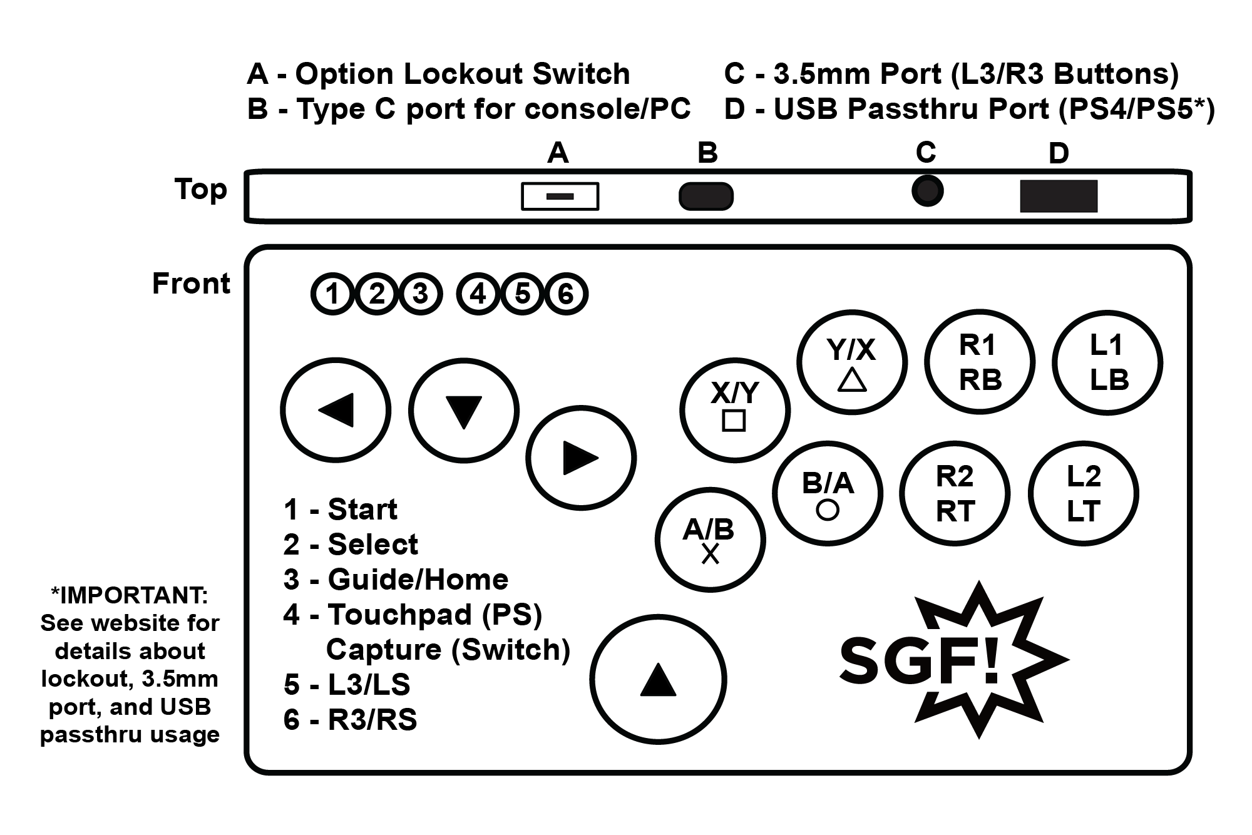
source/configs/SGFDevices/assets/SGF_Layout.png
