duelpadarcade/Duelpad-Zen/source/configs/SparkFunProMicro/assets/SparkFunProMicroRP2040.png

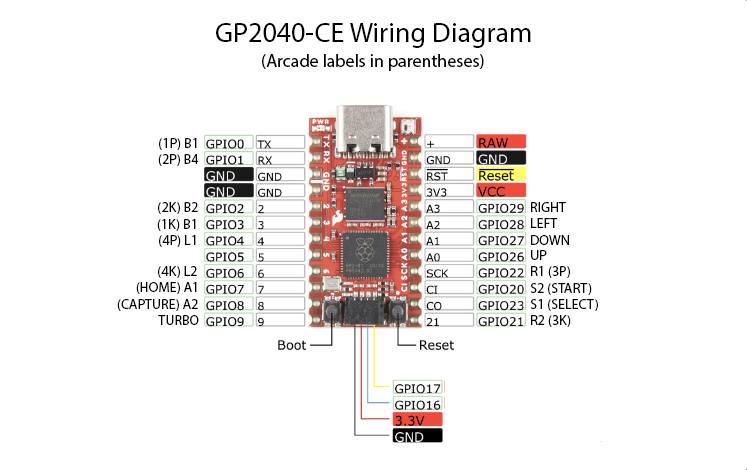
source/configs/SparkFunProMicro/assets/SparkFunProMicroRP2040.png
