duelpadarcade/Duelpad-Zen/source/configs/Stress/assets/stress-00.jpg

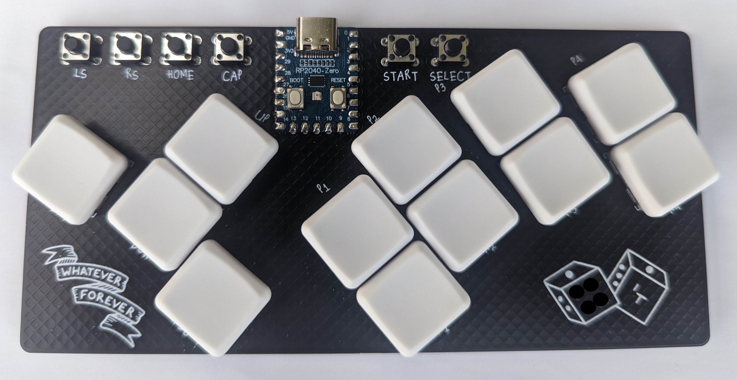
source/configs/Stress/assets/stress-00.jpg
