duelpadarcade/Duelpad-Zen/source/configs/ZeroRhythm/Assets/ZeroRhythm 1.jpg

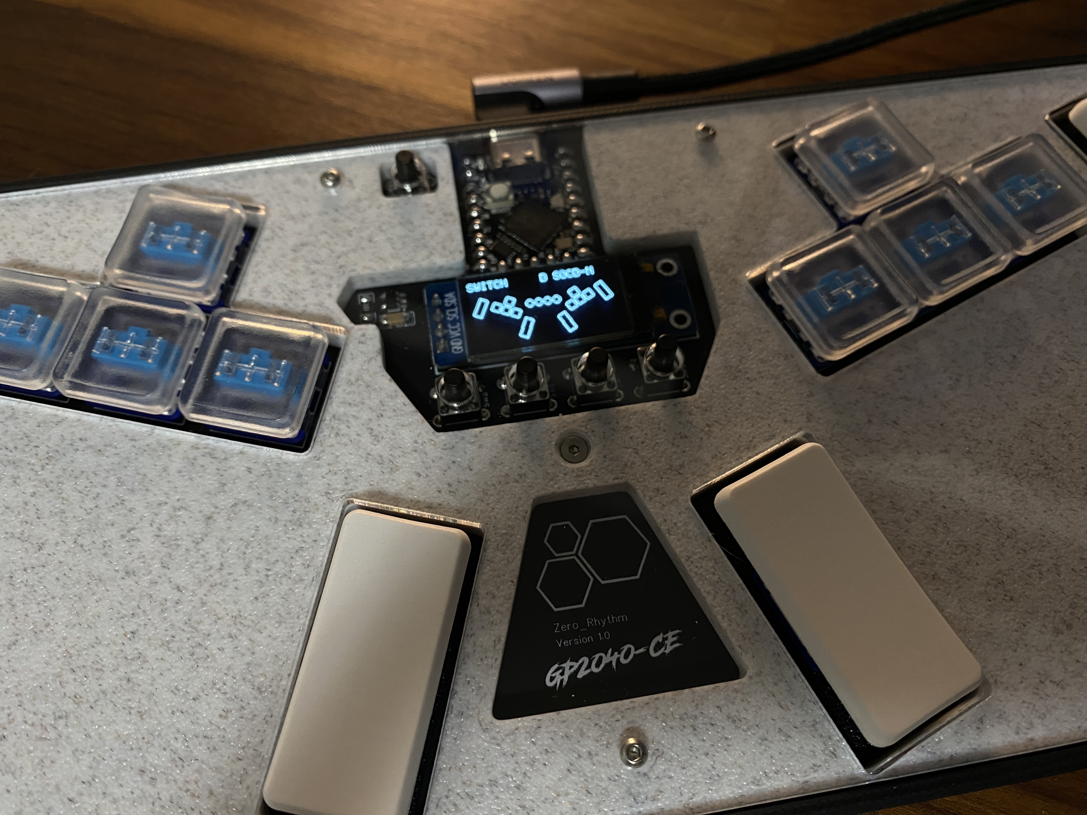
source/configs/ZeroRhythm/Assets/ZeroRhythm 1.jpg
