duelpadarcade/Duelpad-Zen/source/configs/ZeroRhythm/Assets/ZeroThythm 2.jpg

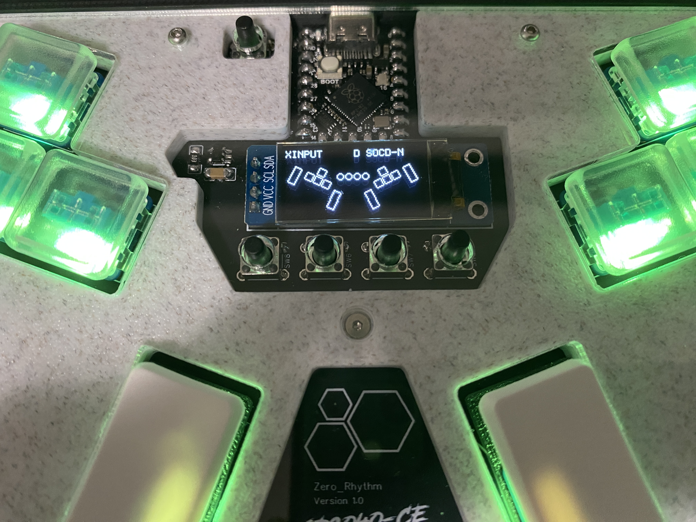
source/configs/ZeroRhythm/Assets/ZeroThythm 2.jpg
