duelpadarcade/Duelpad-Zen/source/configs/OpenCore0/assets/Open_Core0_LED_order.png

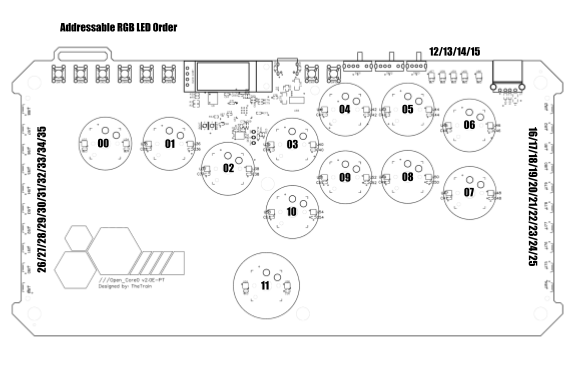
source/configs/OpenCore0/assets/Open_Core0_LED_order.png
