duelpadarcade/Duelpad-Zen/source/src/display/ui/screens/PinViewerScreen.cpp

#include "PinViewerScreen.h"

#include "pico/stdlib.h"

void PinViewerScreen::init() {
    getRenderer()->clearScreen();
}

void PinViewerScreen::shutdown() {
    clearElements();
}

void PinViewerScreen::drawScreen() {
    Mask_t pinValues = ~gpio_get_all();
    GpioMappingInfo* pinMappings = Storage::getInstance().getProfilePinMappings();

    std::string pinsPressed = "PIN: ";
    std::string pinsInUse = "In Use: ";
    std::string pinsUndefined = "Undef: ";
    std::string buttonsPressed = "BTN: ";

    getRenderer()->drawText(5, 0, "[Pin Viewer]");

    for (Pin_t pin = 0; pin < (Pin_t)NUM_BANK0_GPIOS; pin++) {
        if ((pinMappings[pin].action > 0) && (pinMappings[pin].action != GpioAction::CUSTOM_BUTTON_COMBO)) {
            if ((pinValues >> pin) & 0x01) {
                pinsPressed += std::to_string(pin);
                pinsPressed += " ";

                const char * action = buttonLookup[pinMappings[pin].action];
                buttonsPressed += action;
                buttonsPressed += " ";
            }
        } else {
            if (pinMappings[pin].action != GpioAction::NONE) {
                pinsInUse += std::to_string(pin);
                pinsInUse += " ";
            } else {
                pinsUndefined += std::to_string(pin);
                pinsUndefined += " ";
            }
        }
    }

    getRenderer()->drawText(0, 2, pinsUndefined.c_str());
    getRenderer()->drawText(0, 3, pinsInUse.c_str());
    getRenderer()->drawText(0, 4, pinsPressed.c_str());
    getRenderer()->drawText(0, 5, buttonsPressed.c_str());

    getRenderer()->drawText(4, 7, "A1 to Return");
}

int8_t PinViewerScreen::update() {
    if (Storage::getInstance().GetConfigMode()) {
        uint16_t buttonState = getGamepad()->state.buttons;
        if (prevButtonState && !buttonState) {
            if (prevButtonState == GAMEPAD_MASK_A1) {
                prevButtonState = 0;
                return DisplayMode::CONFIG_INSTRUCTION;
            }
        }
        prevButtonState = buttonState;
    }

    return -1; // -1 means no change in screen state
}
